Rando1f/Blink/assests/CAD  images/front view.png

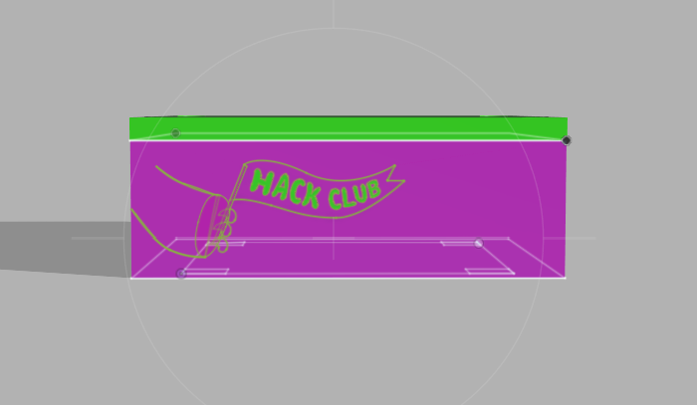
assests/CAD images/front view.png
