Rando1f/Blink/assests/CAD  images/top view.png

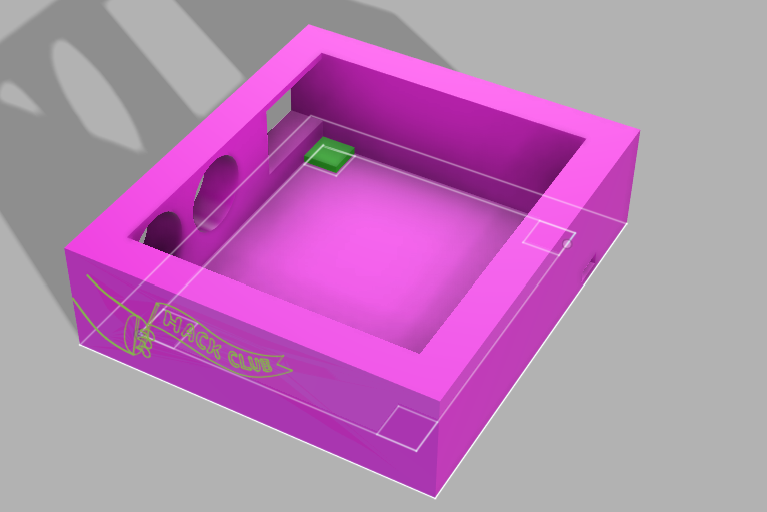
assests/CAD images/top view.png
